mlab-modules/SOLARMINI01/doc/gen/dxf/SOLARMINI01B-F_Fab.dxf

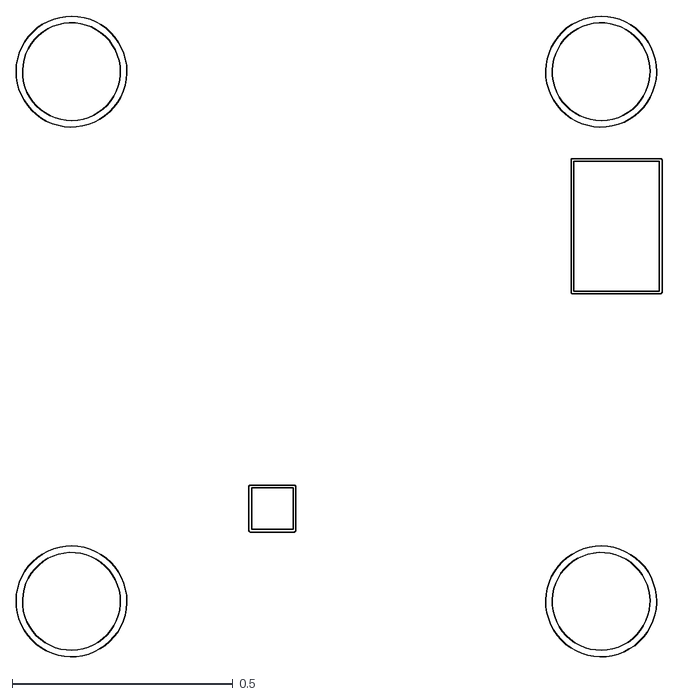
[picture p15: CAD file, 2022-04-06]
doc/gen/dxf/SOLARMINI01B-F_Fab.dxf
1.46 x 1.45
